nesl/locomote/pcb/pcb_images/bat_charger_board_top.png

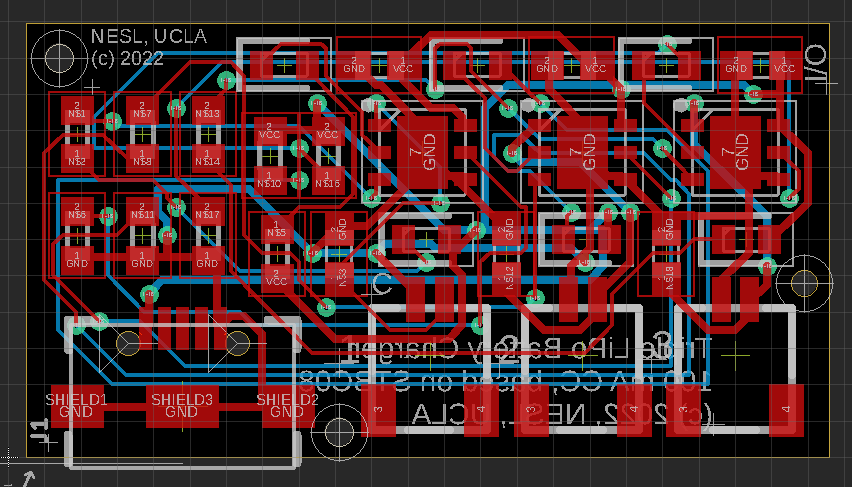
pcb/pcb_images/bat_charger_board_top.png
