nesl/locomote/pcb/pcb_images/bottom_angled_pcb_3D.PNG

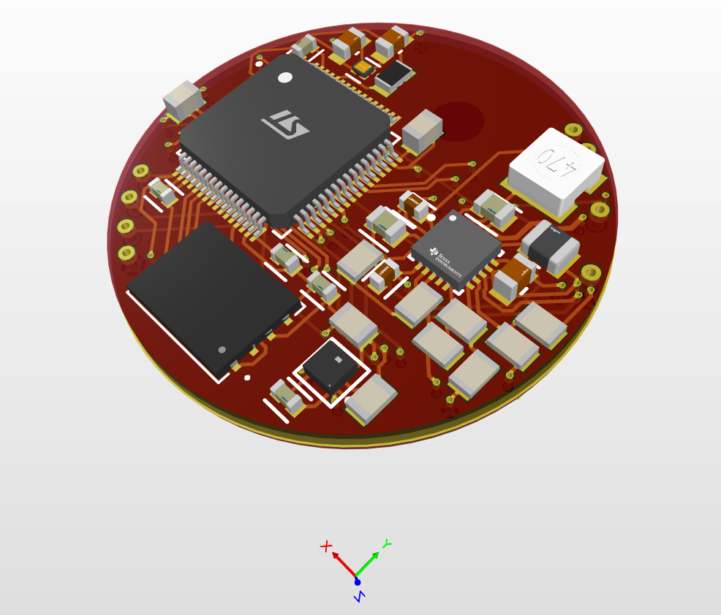
pcb/pcb_images/bottom_angled_pcb_3D.PNG
