nesl/locomote/pcb/pcb_images/bottom_pcb.PNG

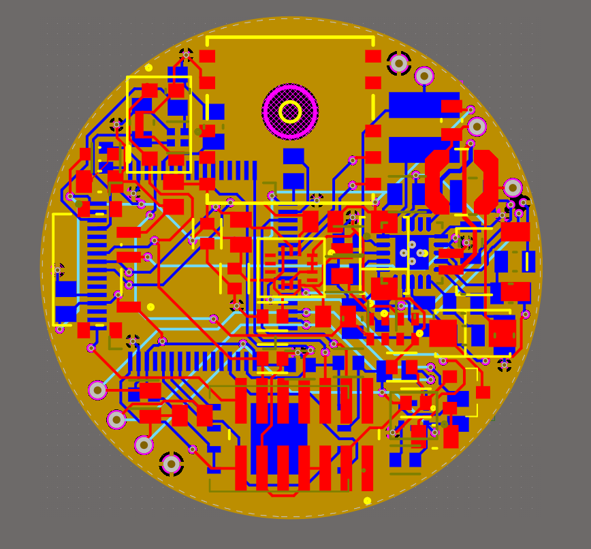
pcb/pcb_images/bottom_pcb.PNG
