nesl/locomote/pcb/pcb_images/bottom_pcb_3D.PNG

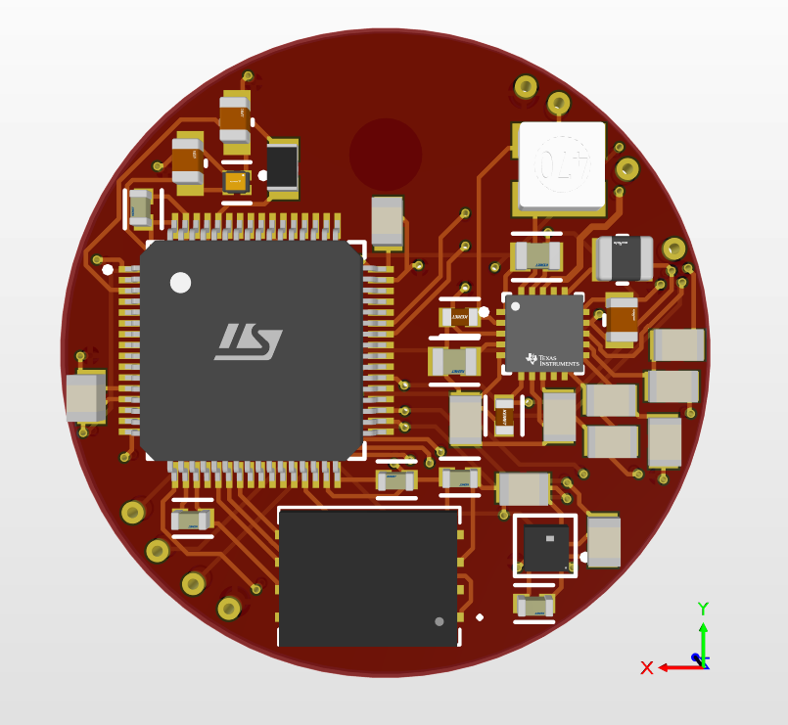
pcb/pcb_images/bottom_pcb_3D.PNG
