nesl/locomote/pcb/pcb_images/bottom_pcb_clean.PNG

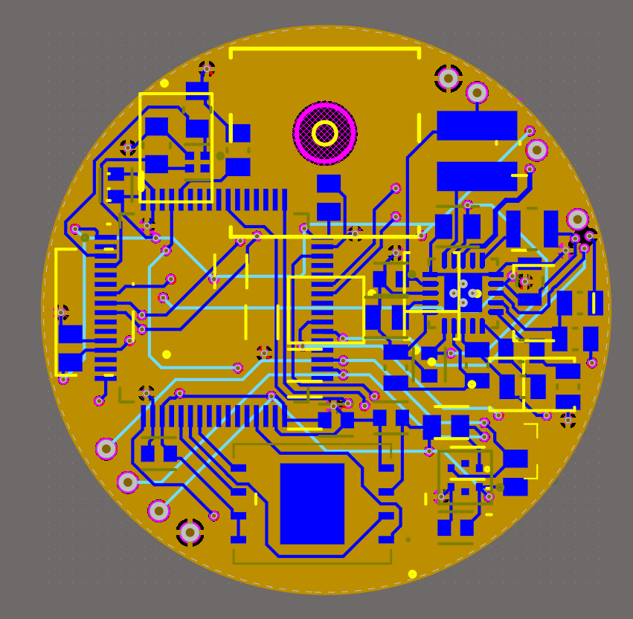
pcb/pcb_images/bottom_pcb_clean.PNG
