nesl/locomote/pcb/pcb_images/pressure_bat_charger_boards_3D.jpg

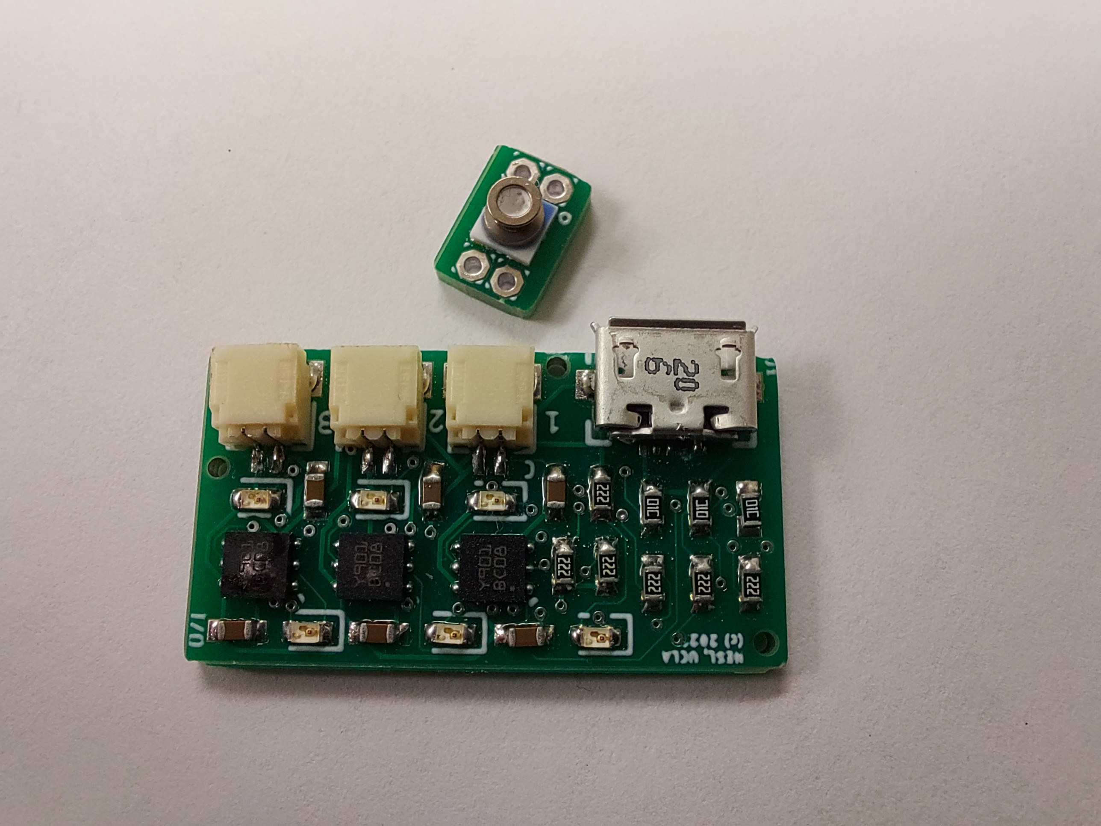
pcb/pcb_images/pressure_bat_charger_boards_3D.jpg
