nesl/locomote/pcb/pcb_images/pressure_board_top.png

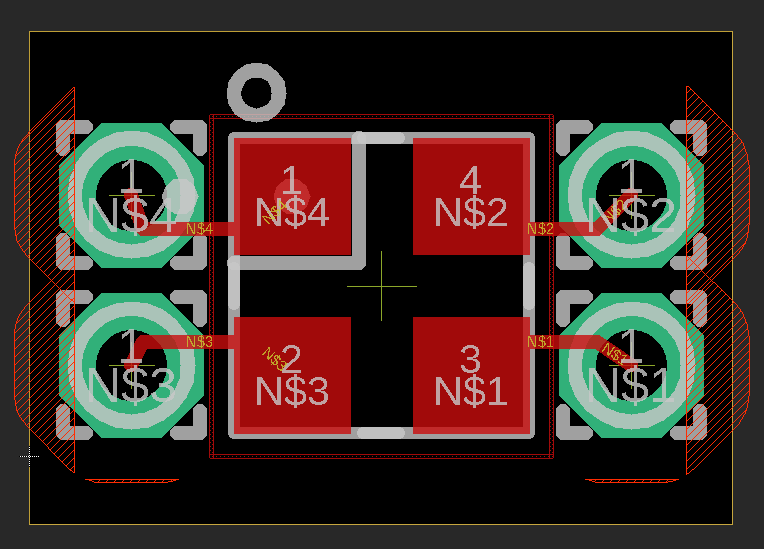
pcb/pcb_images/pressure_board_top.png
