nesl/locomote/pcb/pcb_images/top_pcb.PNG

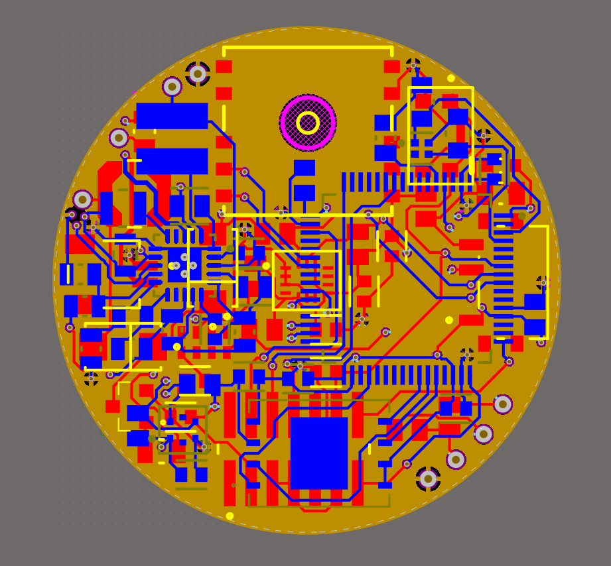
pcb/pcb_images/top_pcb.PNG
