nesl/locomote/pcb/pcb_images/top_pcb_3D.PNG

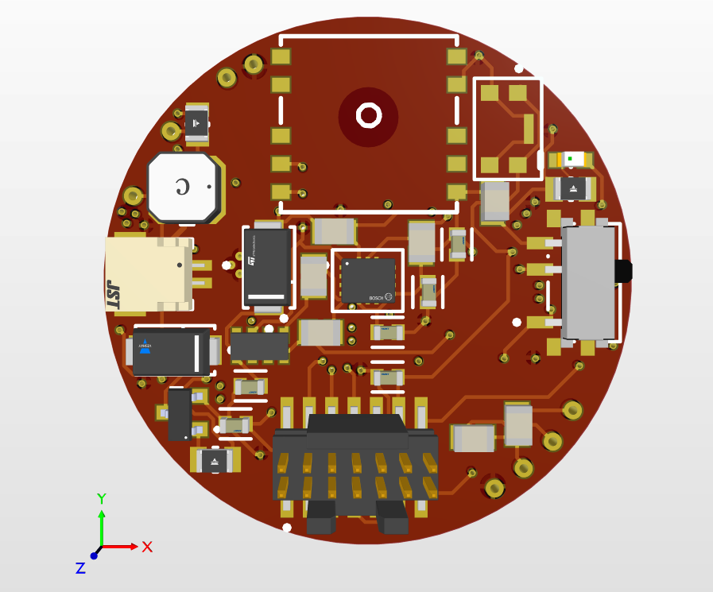
pcb/pcb_images/top_pcb_3D.PNG
