nesl/locomote/pcb/pcb_images/top_pcb_clean.PNG

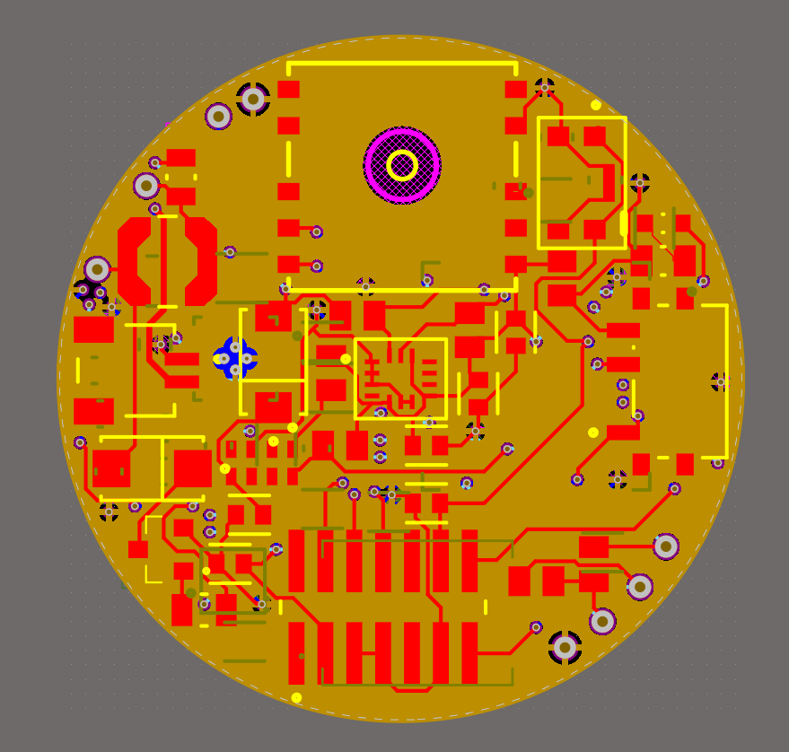
pcb/pcb_images/top_pcb_clean.PNG
