nesl/locomote/pcb/schematic images/mcu_schematic.PNG

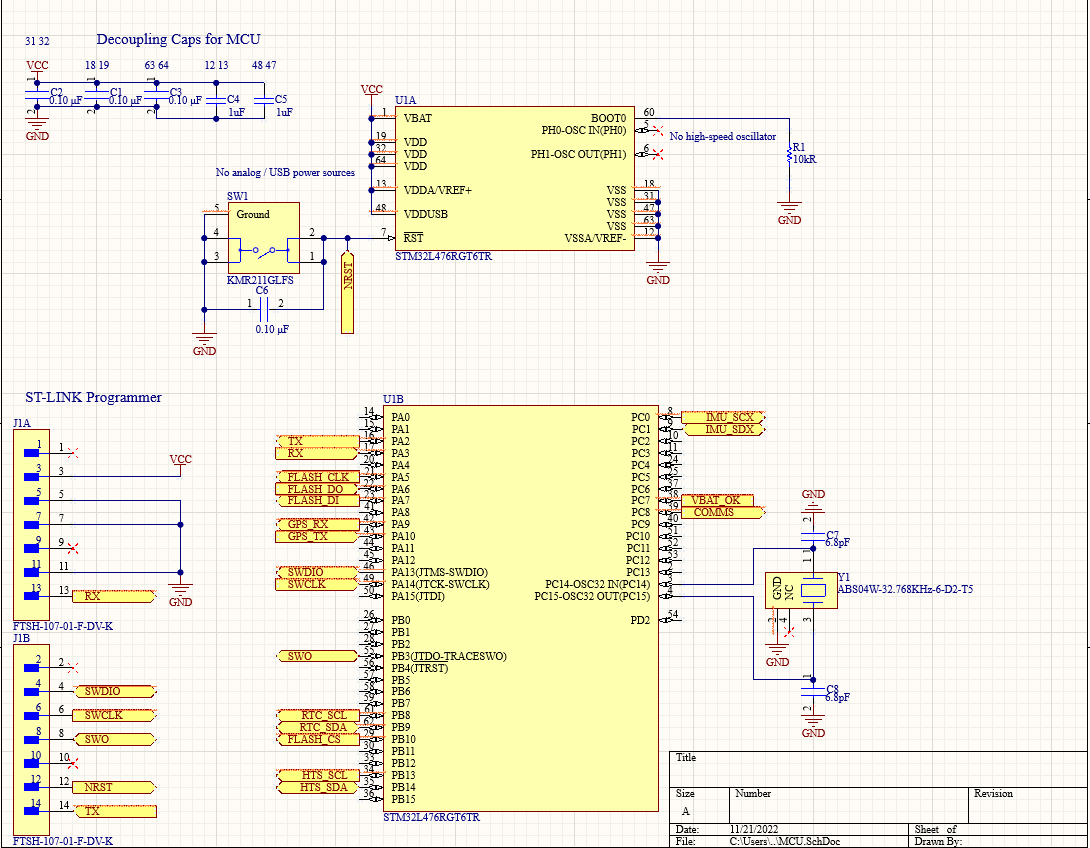
pcb/schematic images/mcu_schematic.PNG
