nesl/locomote/pcb/schematic images/storage_schematic.PNG

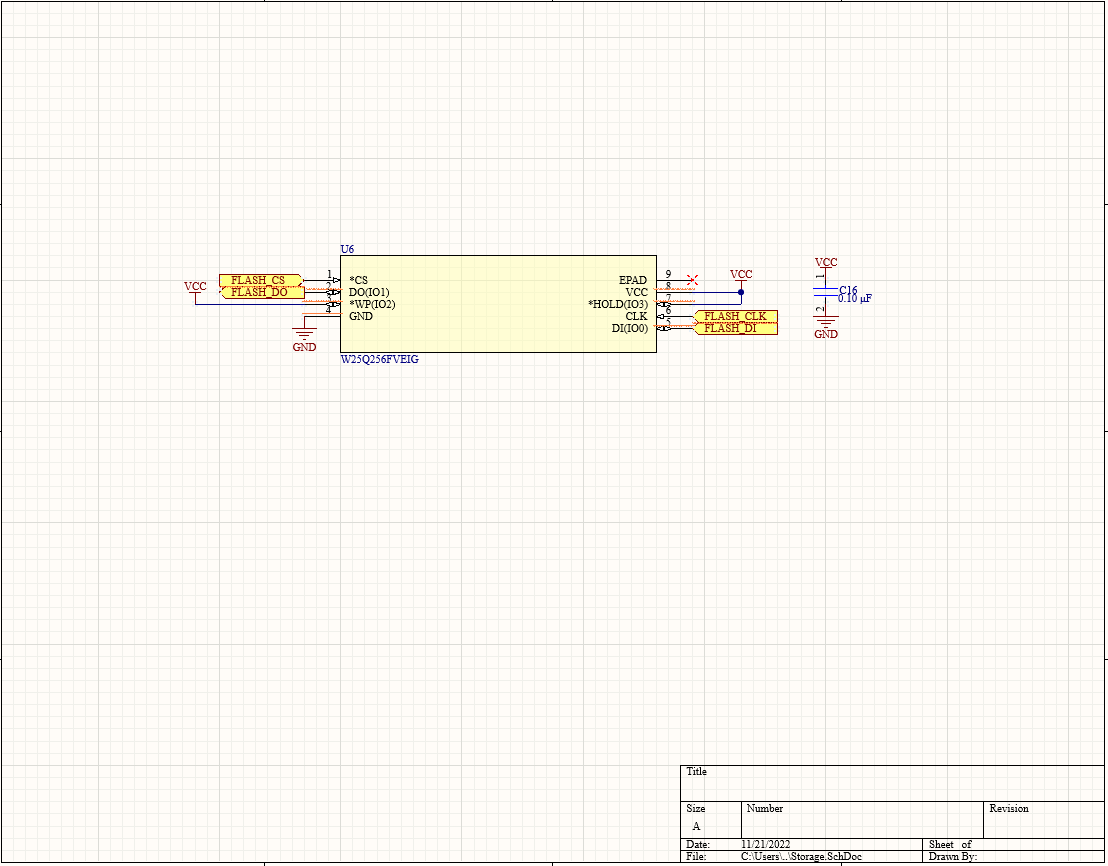
pcb/schematic images/storage_schematic.PNG
